theArnoll/digital-Wi-Fi-clock/PinoutPics/74595.png

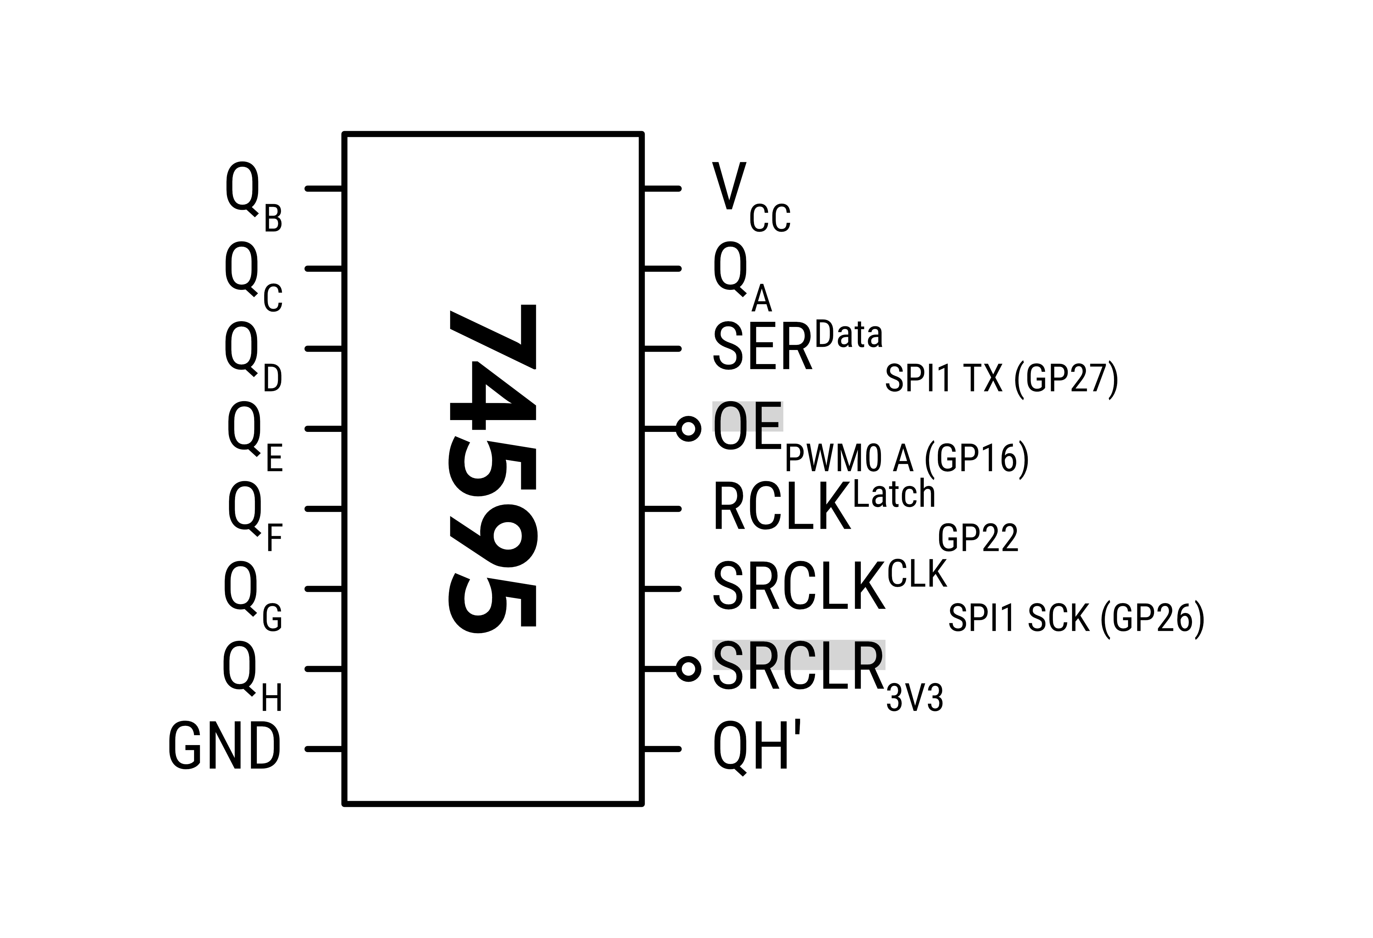
PinoutPics/74595.png
