theArnoll/digital-Wi-Fi-clock/PinoutPics/PinoutsForPrint.png

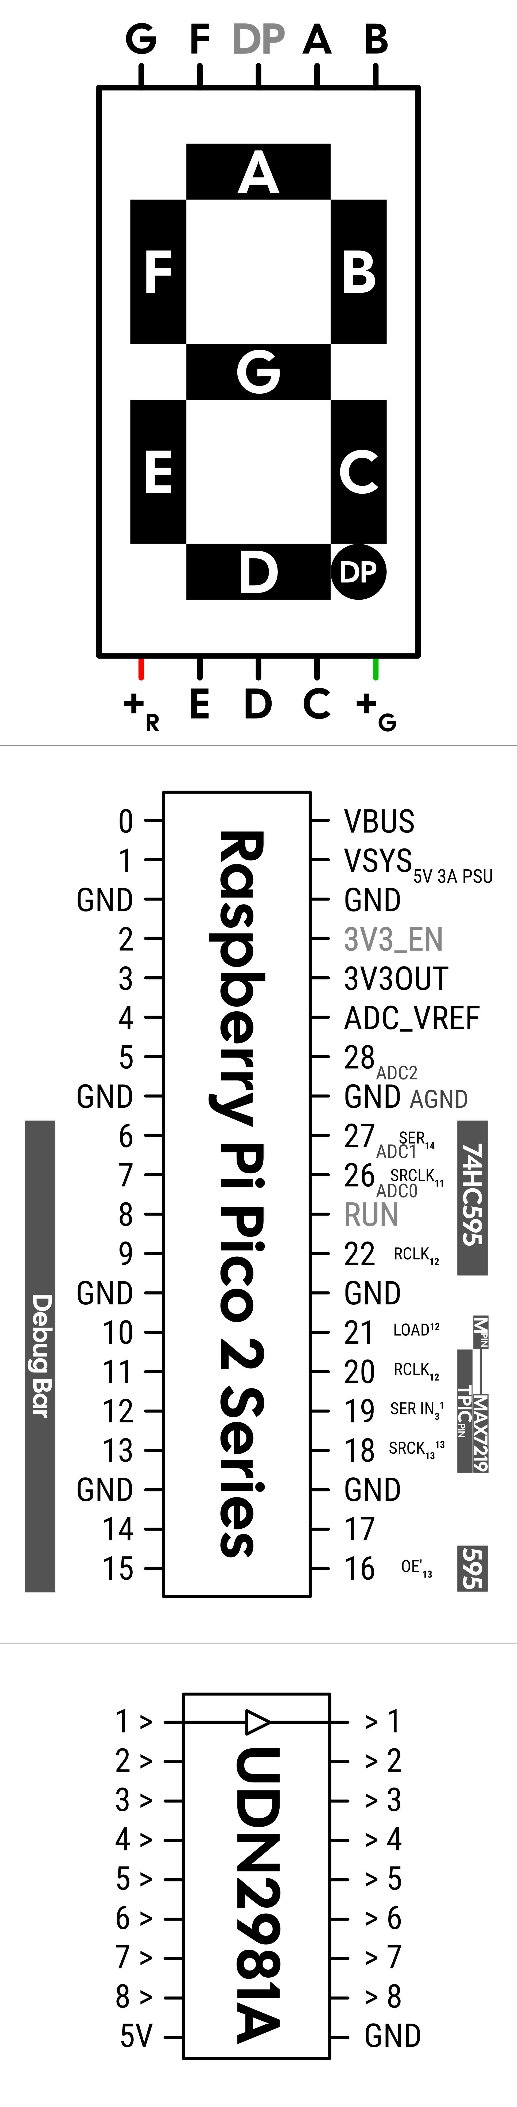
PinoutPics/PinoutsForPrint.png
