theArnoll/digital-Wi-Fi-clock/Schematic/DigitalWiFiClock.kicad_sch

## KiCad design Schematic/DigitalWiFiClock.kicad_sch (2025-12-05)

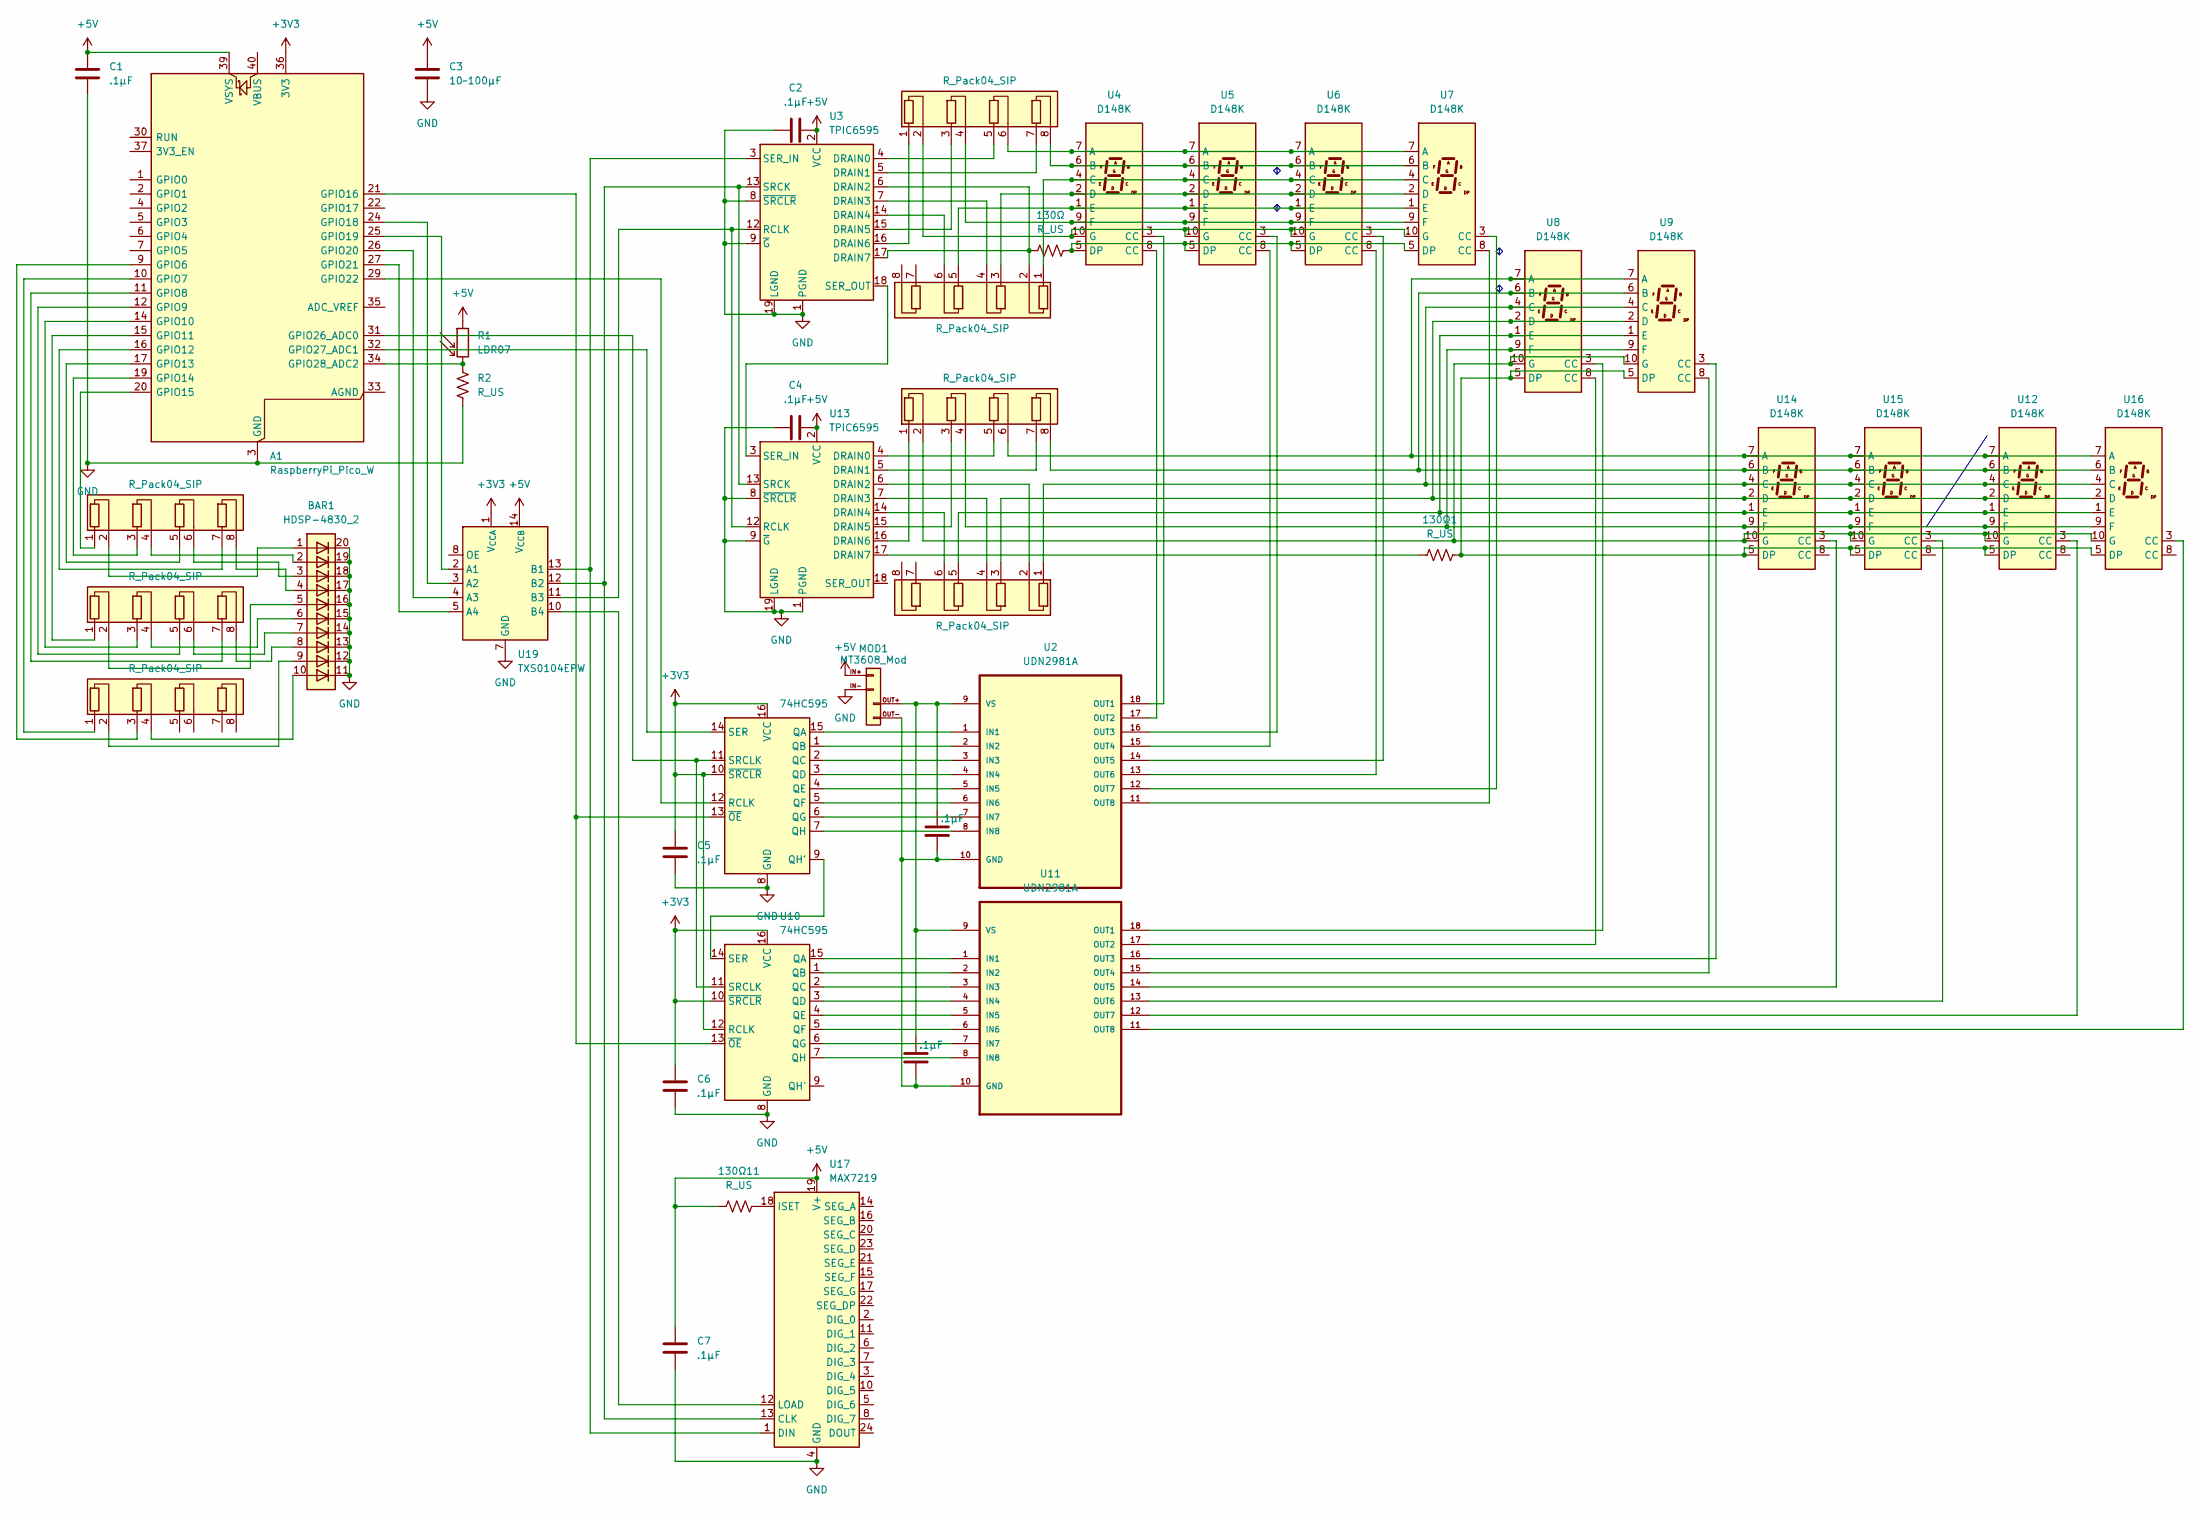
[picture p12: schematic DigitalWiFiClock.kicad_sch]

Parts:
130Ω, 130Ω1, 130Ω11: R_US
A1: RaspberryPi_Pico_W; RaspberryPi_Pico_W_SMD_HandSolder
BAR1: HDSP-4830_2; HDSP-4830
C1, C2, C4, C5, C6, C7, C8, C9: .1μF
C3: 10~100μF
MOD1: MT3608_Mod
R1: LDR07; R_LDR_5.1x4.3mm_P3.4mm_Vertical
R2: R_US
RN1, RN2, RN3, RN4, RN5, RN6, RN7: R_Pack04_SIP; R_Array_SIP8
U1, U10: 74HC595
U2, U11: UDN2981A; DIP254P762X533-18; MPN UDN2981A; DigiKey_Part_Number UDN2981A-ND
U3, U13: TPIC6595
U4, U5, U6, U7, U8, U9, U12, U14, U15, U16: D148K; D1X8K
U17: MAX7219
U19: TXS0104EPW; TSSOP-14_4.4x5mm_P0.65mm

Connections:
+3V3: A1.36 (3V3), C5.2, C6.2, U1.10 (~SRCLR), U1.16 (VCC), U10.10 (~SRCLR), U10.12 (RCLK), U10.16 (VCC), U19.1 (V_{CCA})
+5V: 130Ω11.2, A1.39 (VSYS), C1.1, C2.2, C3.1, C4.2, C7.2, MOD1.IN+ (Pin_1), R1.1, U3.2 (VCC), U13.2 (VCC), U17.19 (V+), U19.14 (V_{CCB})
GND: A1.3 (GND), A1.8 (GND), A1.13 (GND), A1.18 (GND), A1.23 (GND), A1.28 (GND), A1.38 (GND), BAR1.11 (K), BAR1.12 (K), BAR1.13 (K), BAR1.14 (K), BAR1.15 (K), BAR1.16 (K), BAR1.17 (K), BAR1.18 (K), BAR1.19 (K), BAR1.20 (K), C1.2, C2.1, C3.2, C4.1, C5.1, C6.1, C7.1, MOD1.IN- (Pin_2), R2.2, U1.8 (GND), U3.1 (PGND), U3.8 (~SRCLR), U3.9 (~G), U3.10 (PGND), U3.11 (PGND), U3.19 (LGND), U3.20 (PGND), U10.8 (GND), U13.1 (PGND), U13.8 (~SRCLR), U13.9 (~G), U13.10 (PGND), U13.11 (PGND), U13.19 (LGND), U13.20 (PGND), U17.4 (GND), U17.9 (GND), U19.7 (GND)
unnamed: 130Ω1.1, U8.5 (DP), U9.5 (DP), U12.5 (DP), U14.5 (DP), U15.5 (DP), U16.5 (DP)
unnamed: 130Ω1.2, U13.17 (DRAIN7)
unnamed: 130Ω11.1, U17.18 (ISET)
unnamed: 130Ω.1, U4.5 (DP), U5.5 (DP), U6.5 (DP), U7.5 (DP)
unnamed: 130Ω.2, RN2.2 (R1.2), U3.6 (DRAIN2), U3.17 (DRAIN7)
unnamed: A1.9 (GPIO6), RN7.3 (R2.1)
unnamed: A1.10 (GPIO7), RN7.1 (R1.1)
unnamed: A1.11 (GPIO8), RN6.7 (R4.1)
unnamed: A1.12 (GPIO9), RN6.5 (R3.1)
unnamed: A1.14 (GPIO10), RN6.3 (R2.1)
unnamed: A1.15 (GPIO11), RN6.1 (R1.1)
unnamed: A1.16 (GPIO12), RN5.7 (R4.1)
unnamed: A1.17 (GPIO13), RN5.5 (R3.1)
unnamed: A1.19 (GPIO14), RN5.3 (R2.1)
unnamed: A1.20 (GPIO15), RN5.1 (R1.1)
unnamed: A1.21 (GPIO16), U1.13 (~OE), U10.13 (~OE)
unnamed: A1.24 (GPIO18), U19.3 (A2)
unnamed: A1.25 (GPIO19), U19.2 (A1)
unnamed: A1.26 (GPIO20), U19.4 (A3)
unnamed: A1.27 (GPIO21), U19.5 (A4)
unnamed: A1.29 (GPIO22), U1.12 (RCLK)
unnamed: A1.31 (GPIO26_ADC0), U1.11 (SRCLK), U10.11 (SRCLK)
unnamed: A1.32 (GPIO27_ADC1), U1.14 (SER)
unnamed: A1.34 (GPIO28_ADC2), R1.2, R2.1
unnamed: BAR1.1 (A), RN5.2 (R1.2)
unnamed: BAR1.2 (A), RN5.4 (R2.2)
unnamed: BAR1.3 (A), RN5.6 (R3.2)
unnamed: BAR1.4 (A), RN5.8 (R4.2)
unnamed: BAR1.5 (A), RN6.2 (R1.2)
unnamed: BAR1.6 (A), RN6.4 (R2.2)
unnamed: BAR1.7 (A), RN6.6 (R3.2)
unnamed: BAR1.8 (A), RN6.8 (R4.2)
unnamed: BAR1.9 (A), RN7.2 (R1.2)
unnamed: BAR1.10 (A), RN7.4 (R2.2)
unnamed: C8.1, C9.1, MOD1.OUT- (Pin_4), U2.10 (GND), U11.10 (GND)
unnamed: C8.2, C9.2, MOD1.OUT+ (Pin_3), U2.9 (VS), U11.9 (VS)
unnamed: RN1.1 (R1.1), U3.16 (DRAIN6)
unnamed: RN1.2 (R1.2), U4.10 (G), U5.10 (G), U6.10 (G), U7.10 (G)
unnamed: RN1.3 (R2.1), U3.15 (DRAIN5)
unnamed: RN1.4 (R2.2), U4.9 (F), U5.9 (F), U6.9 (F), U7.9 (F)
unnamed: RN1.5 (R3.1), U3.4 (DRAIN0)
unnamed: RN1.6 (R3.2), U4.7 (A), U5.7 (A), U6.7 (A), U7.7 (A)
unnamed: RN1.7 (R4.1), U3.5 (DRAIN1)
unnamed: RN1.8 (R4.2), U4.6 (B), U5.6 (B), U6.6 (B), U7.6 (B)
unnamed: RN2.1 (R1.1), U4.4 (C), U5.4 (C), U6.4 (C), U7.4 (C)
unnamed: RN2.3 (R2.1), U4.2 (D), U5.2 (D), U6.2 (D), U7.2 (D)
unnamed: RN2.4 (R2.2), U3.7 (DRAIN3)
unnamed: RN2.5 (R3.1), U4.1 (E), U5.1 (E), U6.1 (E), U7.1 (E)
unnamed: RN2.6 (R3.2), U3.14 (DRAIN4)
unnamed: RN3.1 (R1.1), U8.4 (C), U9.4 (C), U12.4 (C), U14.4 (C), U15.4 (C), U16.4 (C)
unnamed: RN3.2 (R1.2), U13.6 (DRAIN2)
unnamed: RN3.3 (R2.1), U8.2 (D), U9.2 (D), U12.2 (D), U14.2 (D), U15.2 (D), U16.2 (D)
unnamed: RN3.4 (R2.2), U13.7 (DRAIN3)
unnamed: RN3.5 (R3.1), U8.1 (E), U9.1 (E), U12.1 (E), U14.1 (E), U15.1 (E), U16.1 (E)
unnamed: RN3.6 (R3.2), U13.14 (DRAIN4)
unnamed: RN4.1 (R1.1), U13.16 (DRAIN6)
unnamed: RN4.2 (R1.2), U8.10 (G), U9.10 (G), U12.10 (G), U14.10 (G), U15.10 (G), U16.10 (G)
unnamed: RN4.3 (R2.1), U13.15 (DRAIN5)
unnamed: RN4.4 (R2.2), U8.9 (F), U9.9 (F), U12.9 (F), U14.9 (F), U15.9 (F), U16.9 (F)
unnamed: RN4.5 (R3.1), U13.4 (DRAIN0)
unnamed: RN4.6 (R3.2), U8.7 (A), U9.7 (A), U12.7 (A), U14.7 (A), U15.7 (A), U16.7 (A)
unnamed: RN4.7 (R4.1), U13.5 (DRAIN1)
unnamed: RN4.8 (R4.2), U8.6 (B), U9.6 (B), U12.6 (B), U14.6 (B), U15.6 (B), U16.6 (B)
unnamed: U1.1 (QB), U2.2 (IN2)
unnamed: U1.2 (QC), U2.3 (IN3)
unnamed: U1.3 (QD), U2.4 (IN4)
unnamed: U1.4 (QE), U2.5 (IN5)
unnamed: U1.5 (QF), U2.6 (IN6)
unnamed: U1.6 (QG), U2.7 (IN7)
unnamed: U1.7 (QH), U2.8 (IN8)
unnamed: U1.9 (QH'), U10.14 (SER)
unnamed: U1.15 (QA), U2.1 (IN1)
unnamed: U2.11 (OUT8), U7.8 (CC)
unnamed: U2.12 (OUT7), U7.3 (CC)
unnamed: U2.13 (OUT6), U6.8 (CC)
unnamed: U2.14 (OUT5), U6.3 (CC)
unnamed: U2.15 (OUT4), U5.8 (CC)
unnamed: U2.16 (OUT3), U5.3 (CC)
unnamed: U2.17 (OUT2), U4.8 (CC)
unnamed: U2.18 (OUT1), U4.3 (CC)
unnamed: U10.1 (QB), U11.2 (IN2)
unnamed: U10.2 (QC), U11.3 (IN3)
unnamed: U10.3 (QD), U11.4 (IN4)
unnamed: U10.4 (QE), U11.5 (IN5)
unnamed: U10.5 (QF), U11.6 (IN6)
unnamed: U10.6 (QG), U11.7 (IN7)
unnamed: U10.7 (QH), U11.8 (IN8)
unnamed: U10.15 (QA), U11.1 (IN1)
unnamed: U11.11 (OUT8), U16.3 (CC)
unnamed: U11.12 (OUT7), U12.3 (CC)
unnamed: U11.13 (OUT6), U15.3 (CC)
unnamed: U11.14 (OUT5), U14.3 (CC)
unnamed: U9.8 (CC), U11.15 (OUT4)
unnamed: U9.3 (CC), U11.16 (OUT3)
unnamed: U8.8 (CC), U11.17 (OUT2)
unnamed: U8.3 (CC), U11.18 (OUT1)
unnamed: U3.18 (SER_OUT), U13.3 (SER_IN)
unnamed: U3.12 (RCLK), U13.12 (RCLK), U19.11 (B3)
unnamed: U3.13 (SRCK), U13.13 (SRCK), U17.13 (CLK), U19.12 (B2)
unnamed: U3.3 (SER_IN), U17.1 (DIN), U19.13 (B1)
unnamed: U17.12 (LOAD), U19.10 (B4)
